michalin/Blu-ray-Laser-Scanning-Microscope/schematic/lasermic.kicad_sch

## KiCad design schematic/lasermic.kicad_sch (2023-02-05)

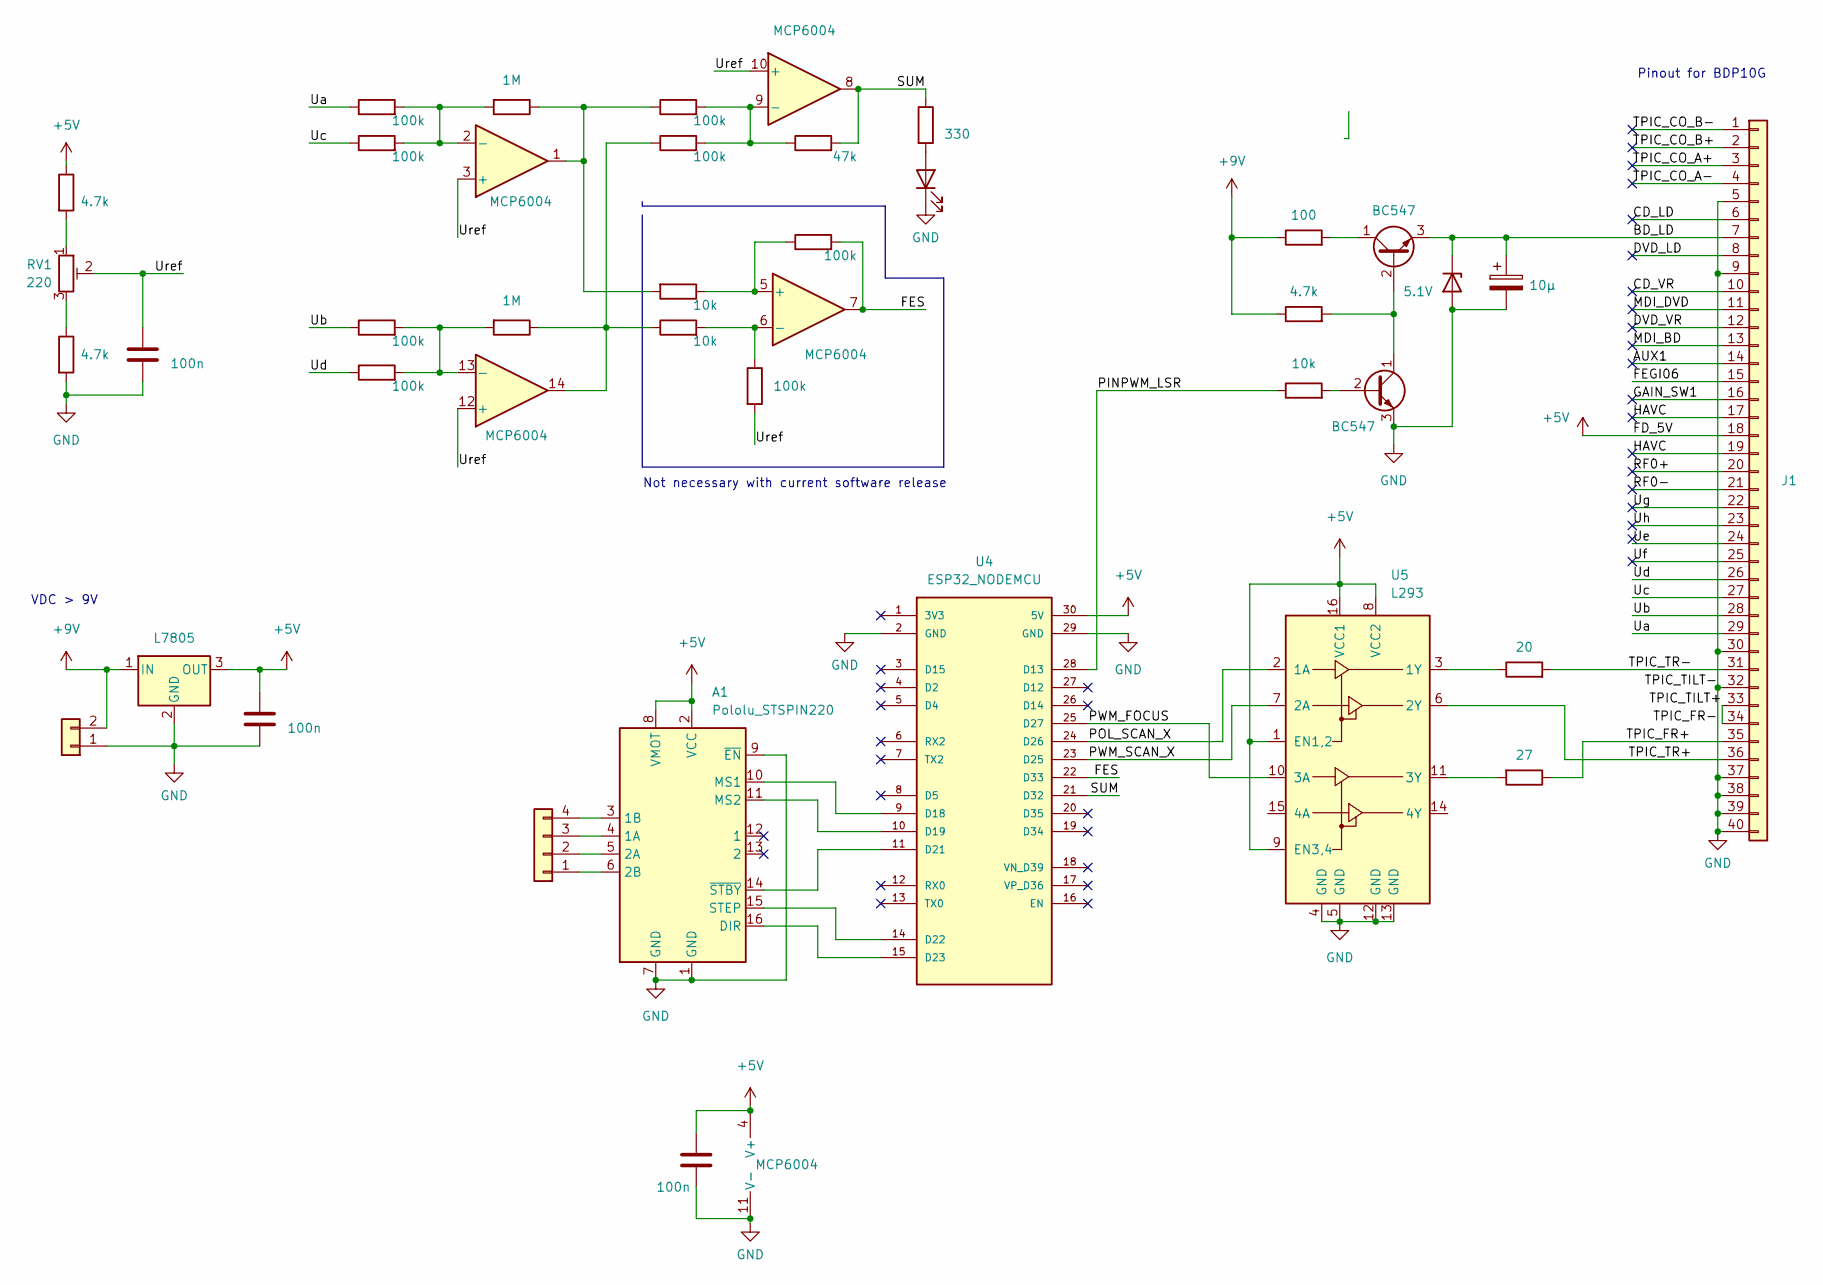
[picture p13: schematic lasermic.kicad_sch]

Parts:
A1: Pololu_STSPIN220; Pololu_Breakout-16_15.2x20.3mm
C1, C6: 100n; C_Disc_D5.0mm_W2.5mm_P2.50mm
C2: 100n; C_Disc_D3.8mm_W2.6mm_P2.50mm
C3: 10µ; CP_Radial_D5.0mm_P2.50mm
D1: LED; LED_D5.0mm
D3: 5.1V; D_DO-41_SOD81_P7.62mm_Horizontal
J1: Hirose_FH12-40S-0.5SH_1x40-1MP_P0.50mm_Horizontal; PinHeader_2x20_P2.54mm_Horizontal
J2: Conn_01x02; PinSocket_1x02_P2.54mm_Vertical
J3: Conn_01x04; PinSocket_1x04_P2.54mm_Vertical
Q1, Q2: BC547; TO-92_Inline
R1: 100; R_Axial_DIN0207_L6.3mm_D2.5mm_P10.16mm_Horizontal
R2, R5: 1M; R_Axial_DIN0207_L6.3mm_D2.5mm_P2.54mm_Vertical
R3, R4, R12: 4.7k; R_Axial_DIN0207_L6.3mm_D2.5mm_P10.16mm_Horizontal
R6, R7, R13: 10k; R_Axial_DIN0207_L6.3mm_D2.5mm_P10.16mm_Horizontal
R8: 100k; R_Axial_DIN0207_L6.3mm_D2.5mm_P10.16mm_Horizontal
R9: 100k; R_Axial_DIN0207_L6.3mm_D2.5mm_P2.54mm_Vertical
R10: 330; R_Axial_DIN0207_L6.3mm_D2.5mm_P10.16mm_Horizontal
R14: 27
RV1: 220; Potentiometer_Piher_PT-10-V10_Vertical
Ra1, Ra2, Ra3, Ra4: 100k; R_Axial_DIN0207_L6.3mm_D2.5mm_P10.16mm_Horizontal
Ra5: 47k; R_Axial_DIN0207_L6.3mm_D2.5mm_P2.54mm_Vertical
Rc1, Rc2: 100k; R_Axial_DIN0207_L6.3mm_D2.5mm_P10.16mm_Horizontal
U2: L7805; TO-220-3_Horizontal_TabDown
U3: MCP6004; DIP-14_W7.62mm
U4: ESP32_NODEMCU; SBC-NodeMCU-ESP32
U5: L293; DIP-16_W7.62mm

Connections:
+5V: A1.2 (VCC), A1.8 (VMOT), C2.1, C6.1, J1.18, R3.1, U2.3 (OUT), U3.4 (V+), U4.30 (5V), U5.1 (EN1,2), U5.8 (VCC2), U5.9 (EN3,4), U5.16 (VCC1)
+9V: J2.2, R1.1, R12.1, U2.1 (IN)
AUX1: J1.14
BD_LD: C3.1, D3.1 (K), J1.7, Q2.3 (E)
CD_LD: J1.6
CD_VR: J1.10
DVD_LD: J1.8
DVD_VR: J1.12
FEGI06: J1.15
FES: R9.2, U3.7, U4.22 (D33)
GAIN_SW1: J1.16
GND: A1.1 (GND), A1.7 (GND), A1.9 (~EN), C1.2, C2.2, C3.2, C6.2, D1.1 (K), D3.2 (A), J1.5, J1.9, J1.30, J1.32, J1.37, J1.38, J1.39, J1.40, J2.1, Q1.3 (E), R4.2, U2.2 (GND), U3.11 (V-), U4.2 (GND), U4.29 (GND), U5.4 (GND), U5.5 (GND), U5.12 (GND), U5.13 (GND)
HAVC: J1.17, J1.19
MDI_BD: J1.13
MDI_DVD: J1.11
unnamed: A1.3 (1B), J3.4
unnamed: A1.4 (1A), J3.3
unnamed: A1.5 (2A), J3.2
unnamed: A1.6 (2B), J3.1
unnamed: A1.10 (MS1), U4.9 (D18)
unnamed: A1.11 (MS2), U4.10 (D19)
unnamed: A1.14 (~STBY), U4.11 (D21)
unnamed: A1.15 (STEP), U4.14 (D22)
unnamed: A1.16 (DIR), U4.15 (D23)
unnamed: D1.2 (A), R10.2
unnamed: Q1.1 (C), Q2.2 (B), R12.2
unnamed: Q1.2 (B), R13.2
unnamed: Q2.1 (C), R1.2
unnamed: R2.1, R6.2, Ra3.1, U3.1
unnamed: R2.2, Ra1.2, Rc1.2, U3.2 (-)
unnamed: R3.2, RV1.1
unnamed: R4.1, RV1.3
unnamed: R5.1, R7.1, Ra4.1, U3.14
unnamed: R5.2, Ra2.2, Rc2.2, U3.13 (-)
unnamed: R6.1, R9.1, U3.5 (+)
unnamed: R7.2, R8.1, U3.6 (-)
unnamed: R14.2, U5.11 (3Y)
unnamed: Ra3.2, Ra4.2, Ra5.1, U3.9 (-)
PINPWM_LSR: R13.1, U4.28 (D13)
POL_SCAN_X: U4.24 (D26), U5.2 (1A)
PWM_FOCUS: U4.25 (D27), U5.10 (3A)
PWM_SCAN_X: U4.23 (D25), U5.7 (2A)
RF0+: J1.20
RF0-: J1.21
SUM: R10.1, Ra5.2, U3.8, U4.21 (D32)
TPIC_CO_A+: J1.3
TPIC_CO_A-: J1.4
TPIC_CO_B+: J1.2
TPIC_CO_B-: J1.1
TPIC_FR+: J1.35, R14.1
TPIC_TILT+: J1.33, J1.34
TPIC_TR+: J1.36, U5.6 (2Y)
TPIC_TR-: J1.31
Ua: J1.29, Ra1.1
Ub: J1.28, Ra2.1
Uc: J1.27, Rc1.1
Ud: J1.26, Rc2.1
Ue: J1.24
Uf: J1.25
Ug: J1.22
Uh: J1.23
Uref: C1.1, R8.2, RV1.2, U3.3 (+), U3.10 (+), U3.12 (+)

Notes on the sheet:
Pinout for BDP10G
Not necessary with current software release
VDC > 9V
